na103/Dueottosei/img/GaryAdapter/socket.jpg

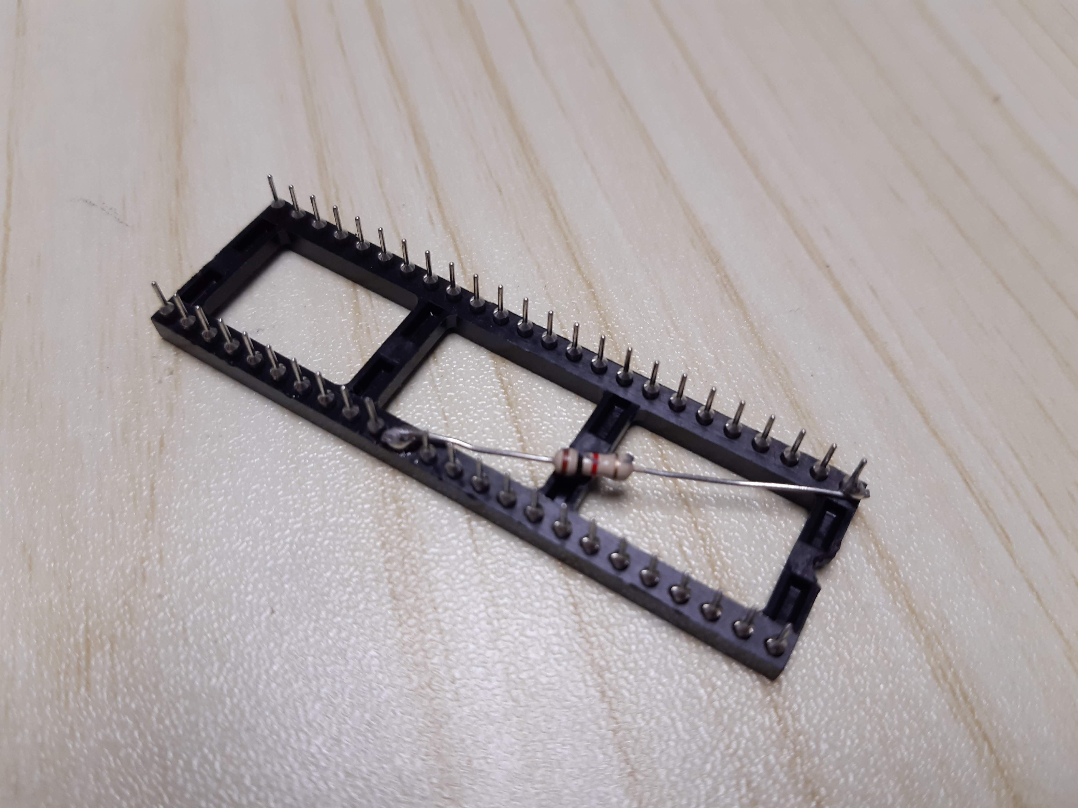
img/GaryAdapter/socket.jpg
