na103/Dueottosei/img/ProgramManager.jpg

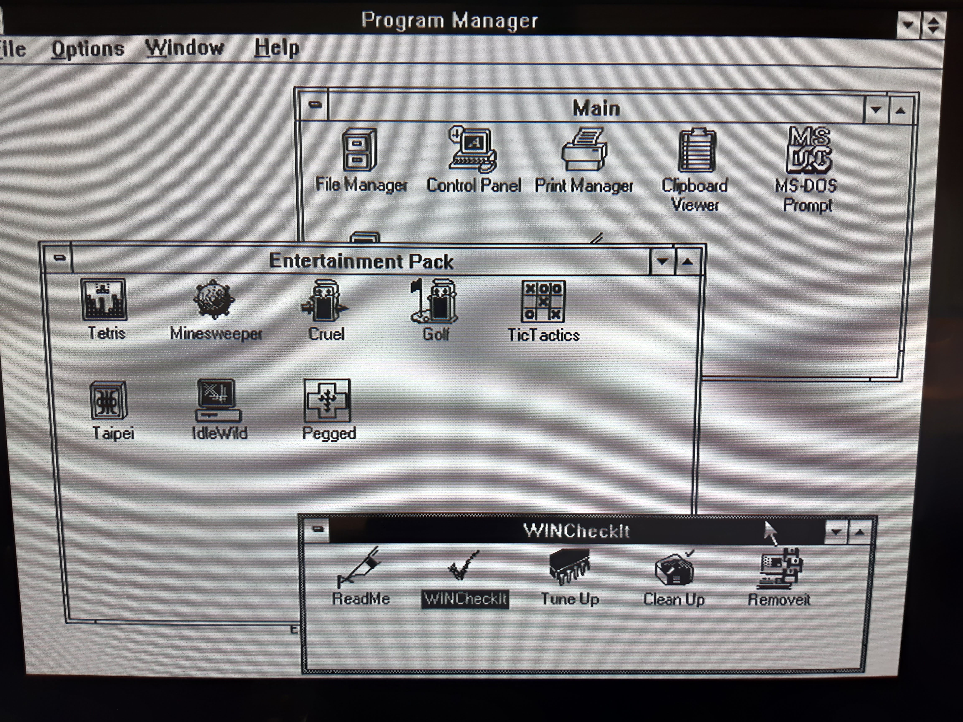
img/ProgramManager.jpg
