na103/Dueottosei/img/routing_B.png

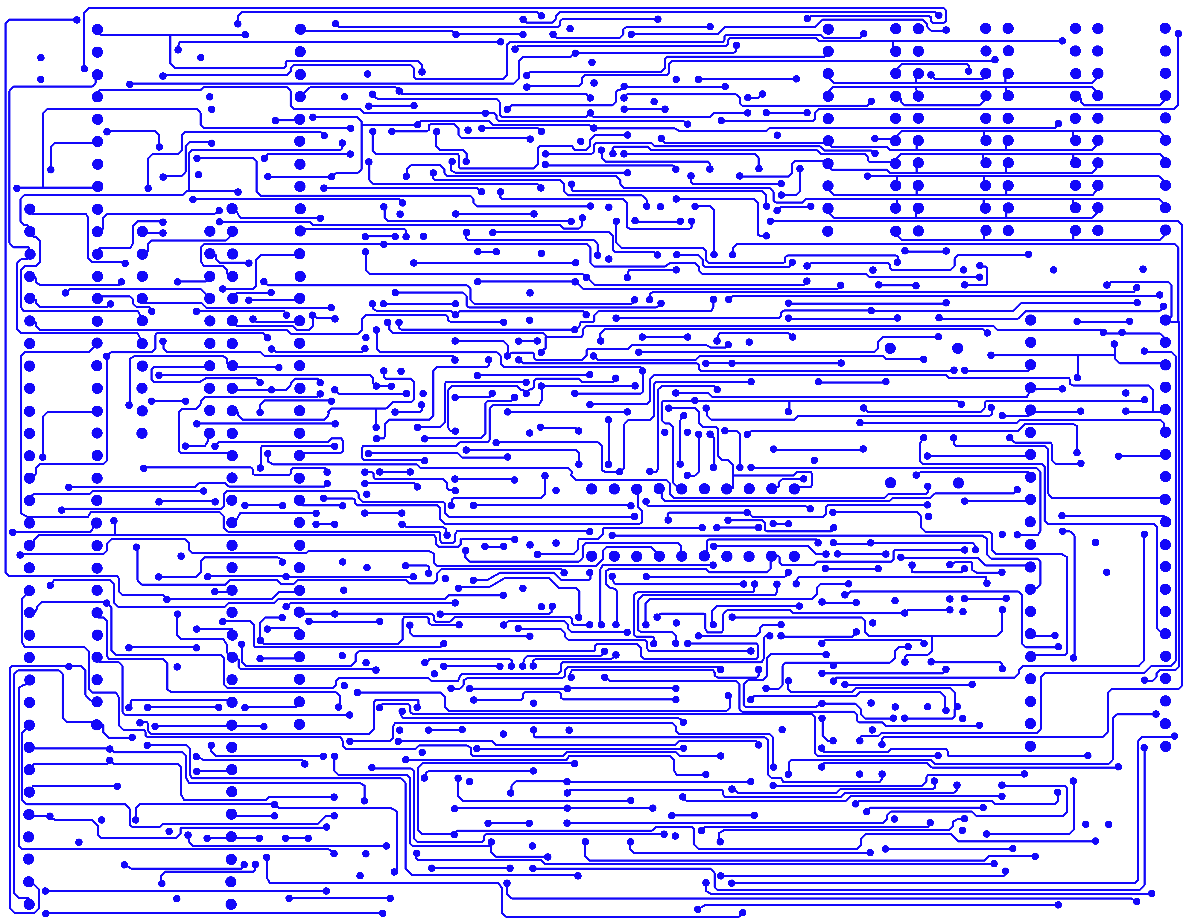
img/routing_B.png
