na103/Dueottosei/img/Wincheckit/cmos.jpg

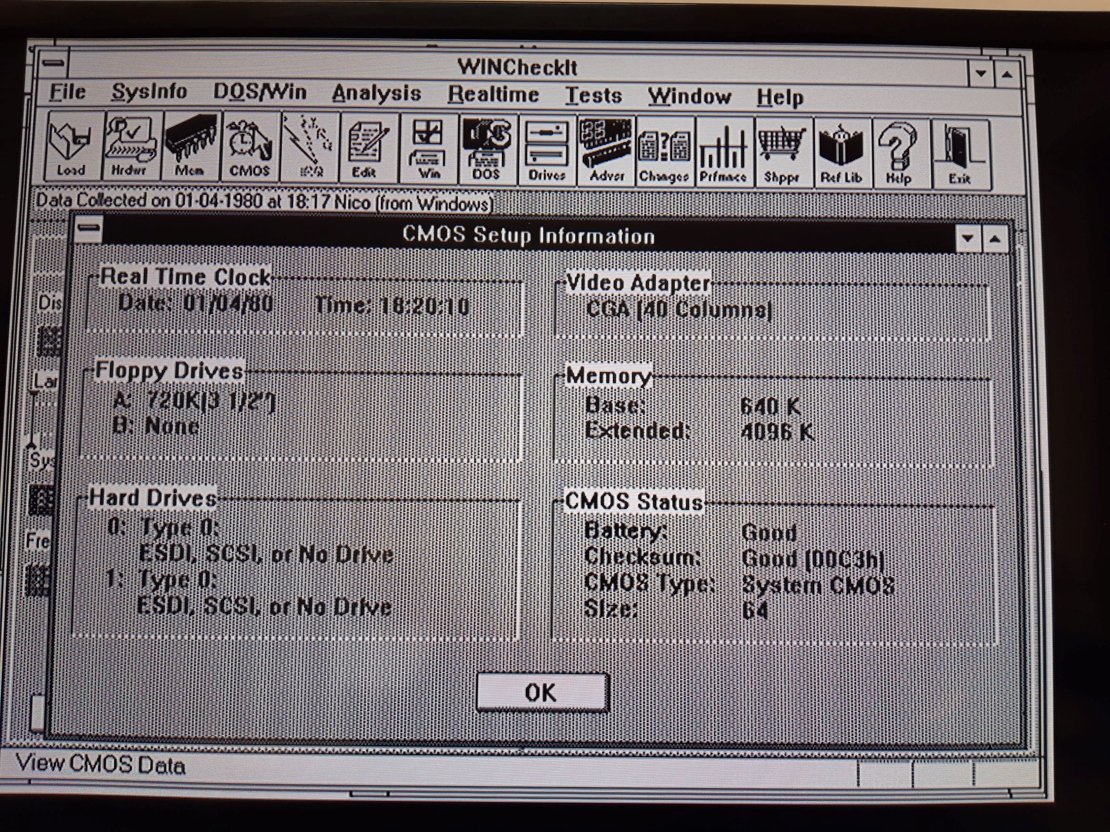
img/Wincheckit/cmos.jpg
