na103/Dueottosei/img/Wincheckit/hw1.jpg

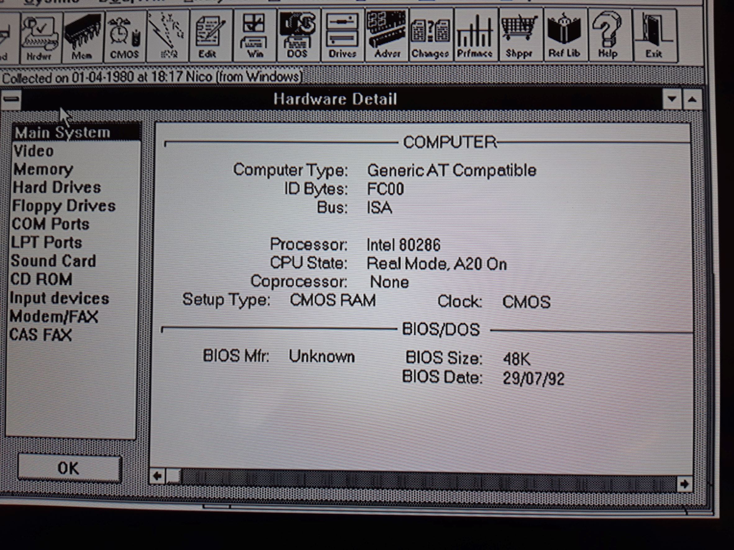
img/Wincheckit/hw1.jpg
