na103/Dueottosei/img/Wincheckit/hw2.jpg

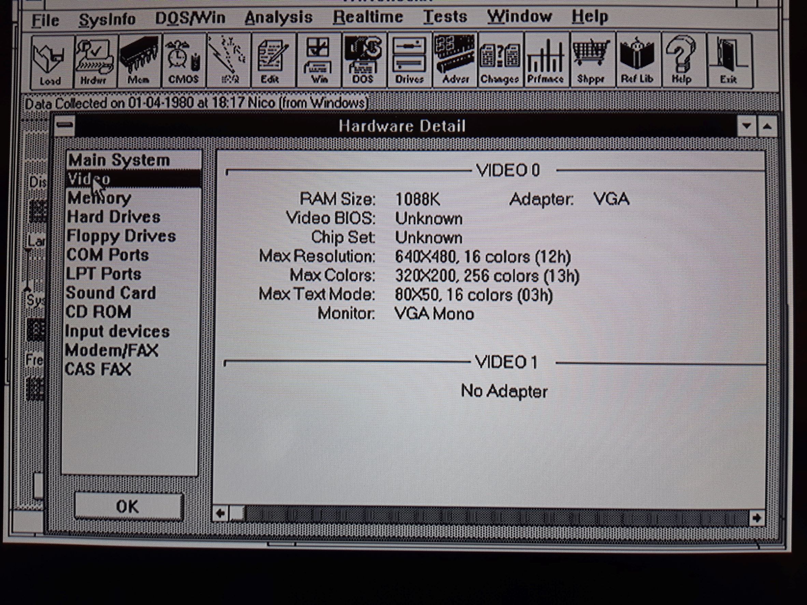
img/Wincheckit/hw2.jpg
