na103/Dueottosei/img/Wincheckit/hw3.jpg

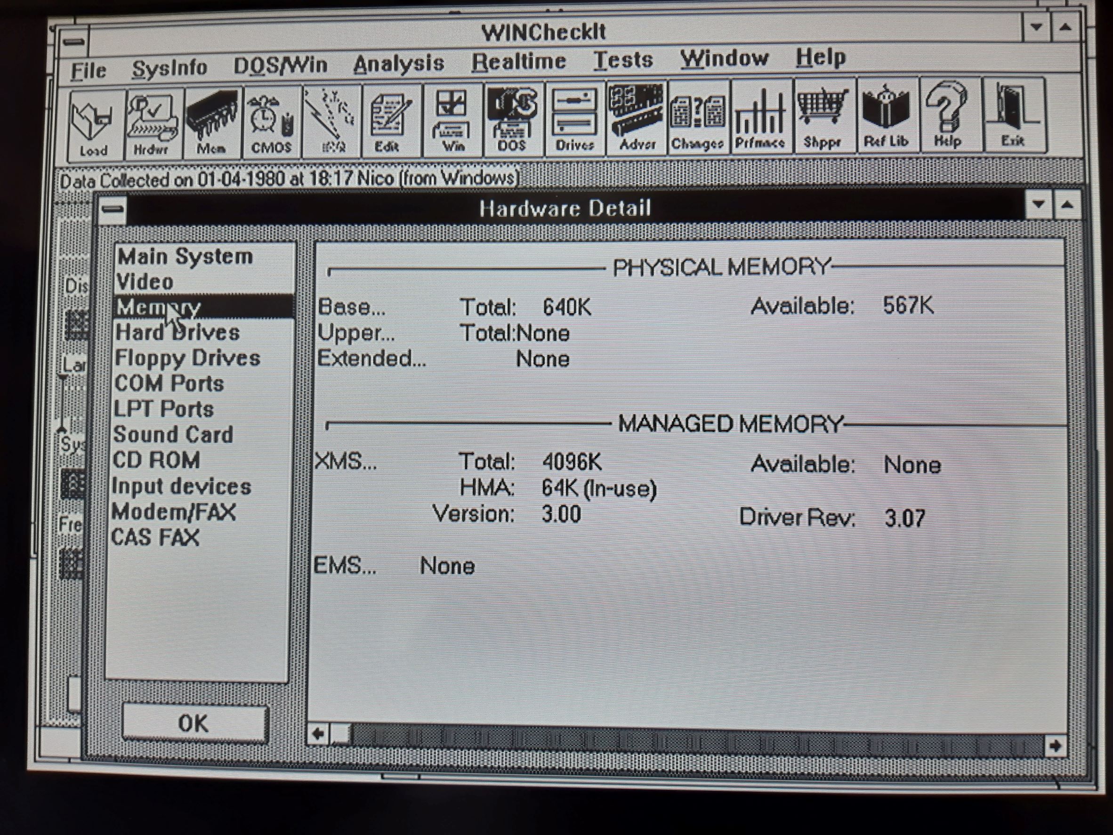
img/Wincheckit/hw3.jpg
