na103/Dueottosei/img/Wincheckit/hw4.jpg

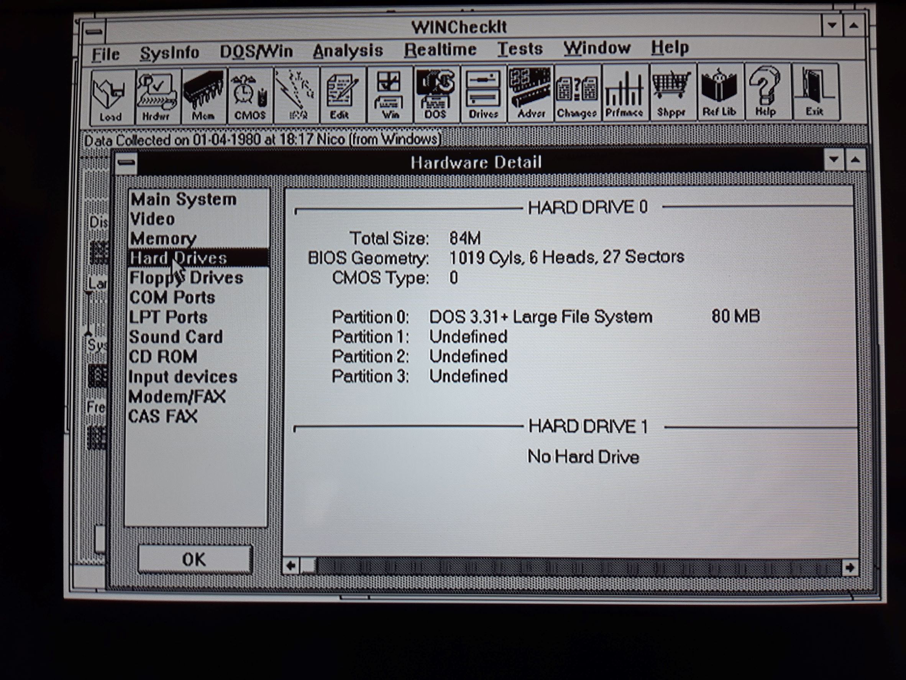
img/Wincheckit/hw4.jpg
