na103/Dueottosei/img/Wincheckit/hw6.jpg

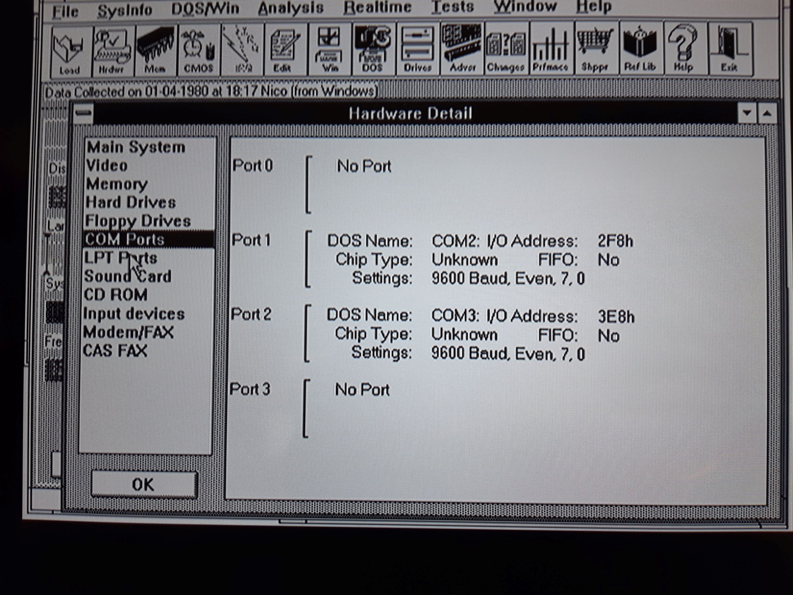
img/Wincheckit/hw6.jpg
