na103/Dueottosei/img/Wincheckit/hw7.jpg

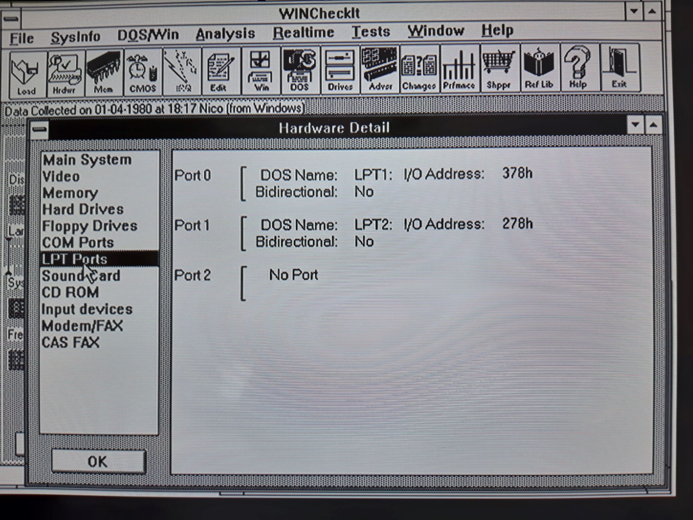
img/Wincheckit/hw7.jpg
