na103/Dueottosei/img/Wincheckit/hw8.jpg

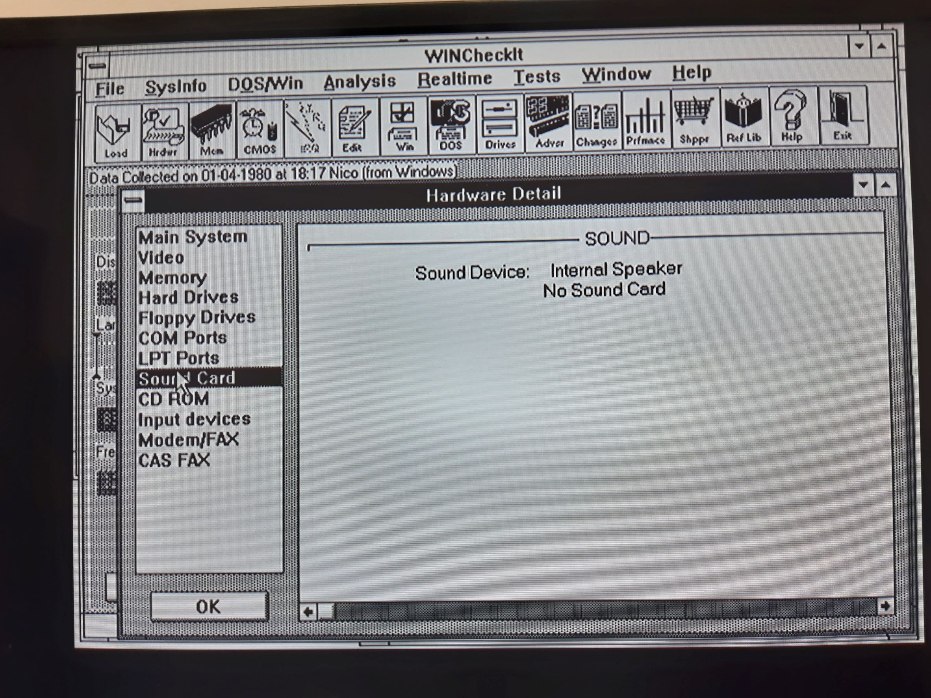
img/Wincheckit/hw8.jpg
