na103/Dueottosei/img/Wincheckit/mem1.jpg

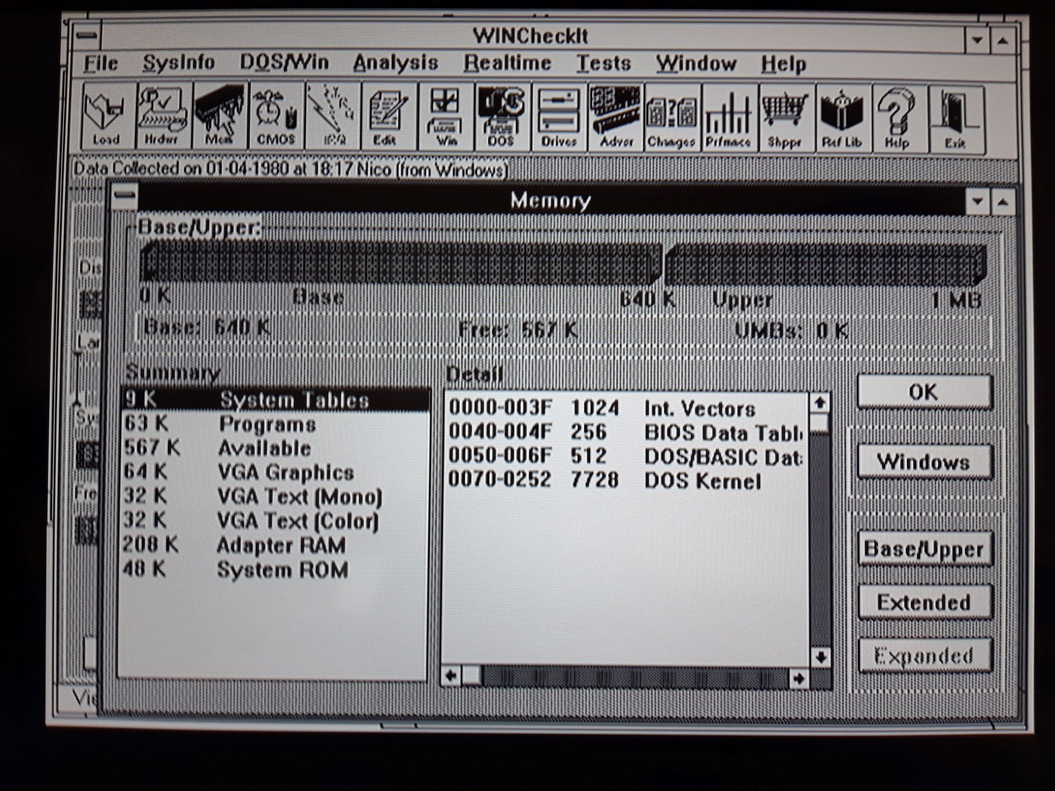
img/Wincheckit/mem1.jpg
