na103/Dueottosei/img/Wincheckit/mem2.jpg

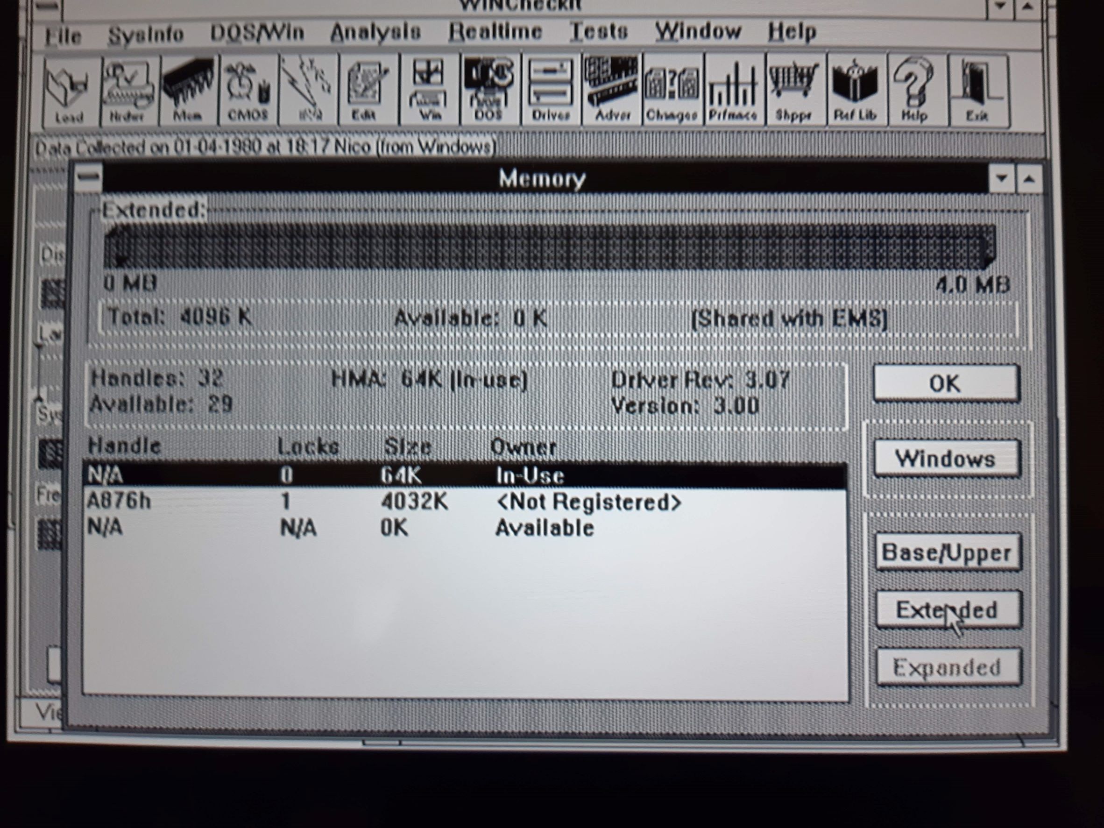
img/Wincheckit/mem2.jpg
