na103/Dueottosei/img/Wincheckit/perf1.jpg

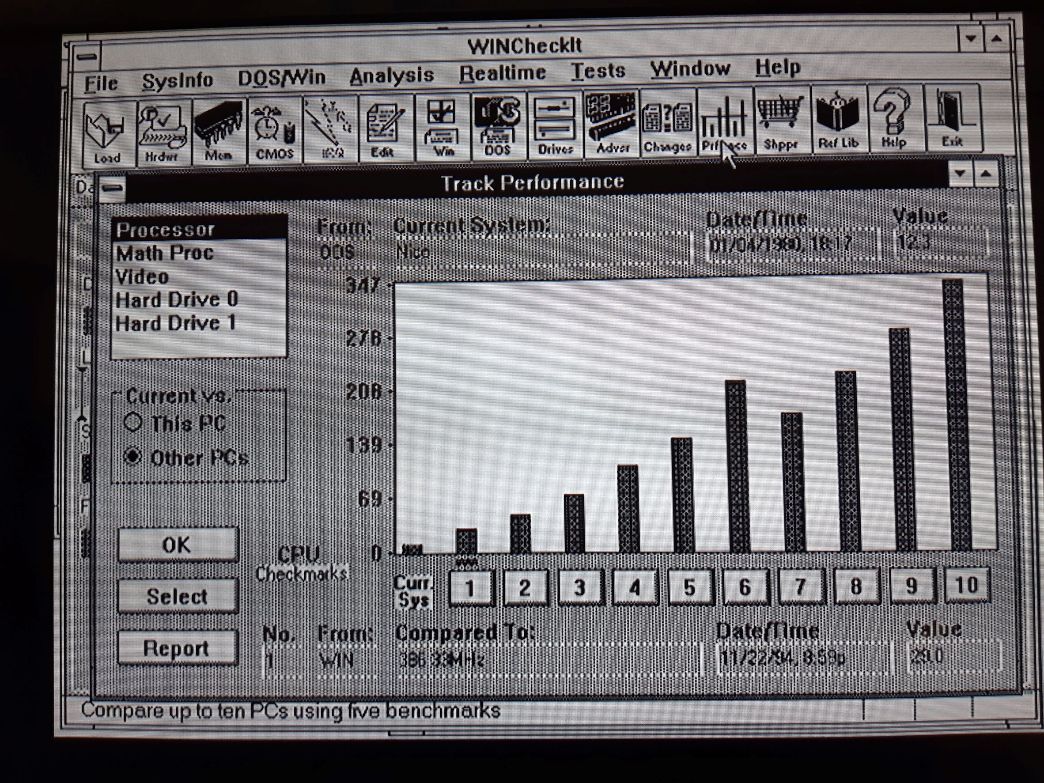
img/Wincheckit/perf1.jpg
