na103/Dueottosei/img/Wincheckit/perf3.jpg

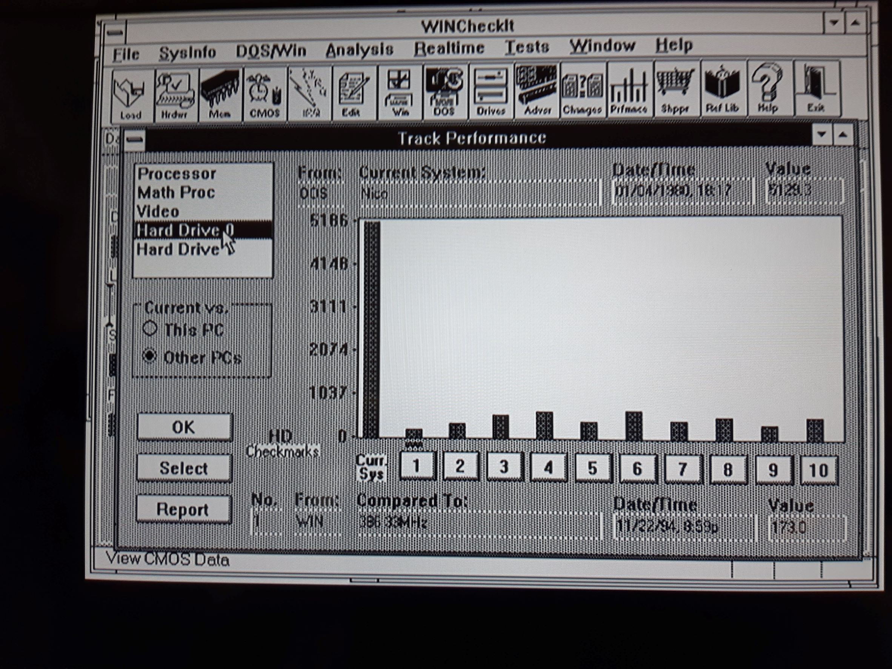
img/Wincheckit/perf3.jpg
