na103/Dueottosei/img/Wincheckit/summary.jpg

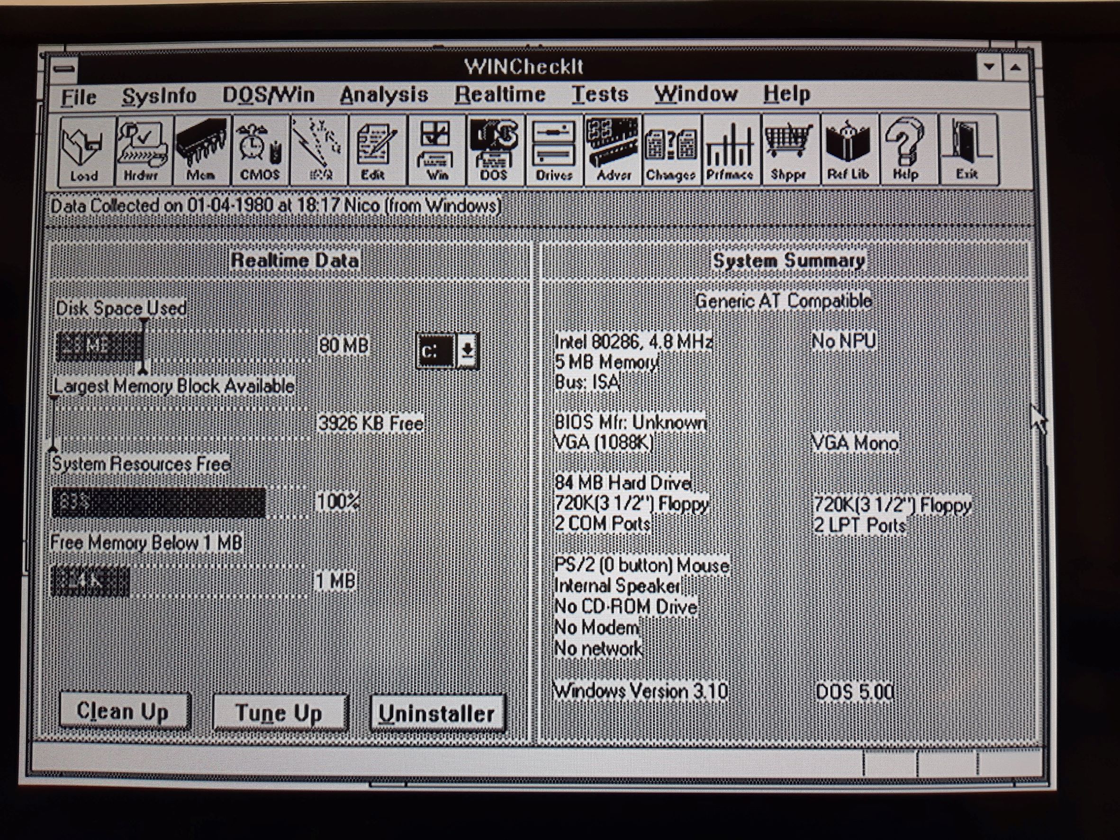
img/Wincheckit/summary.jpg
