na103/Dueottosei/img/Word2.0.jpg

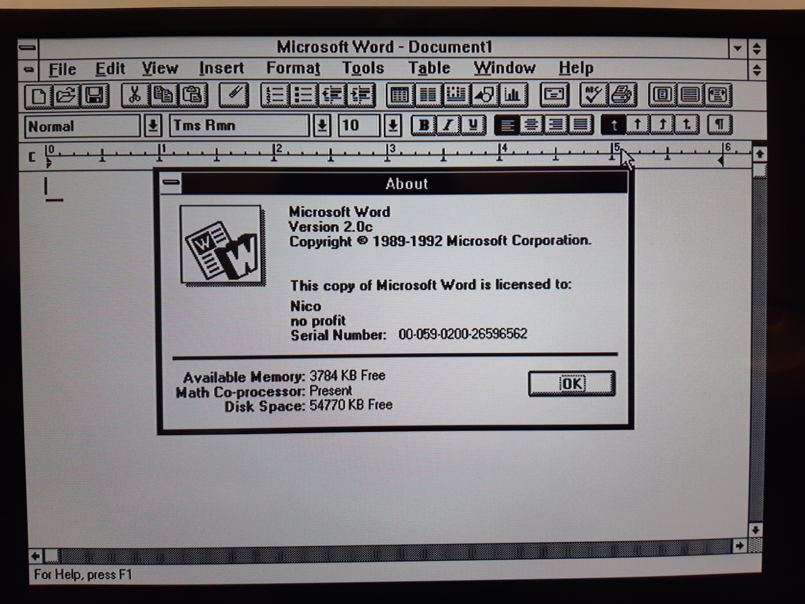
img/Word2.0.jpg
