na103/Dueottosei/img/xc2018_vortex.jpg

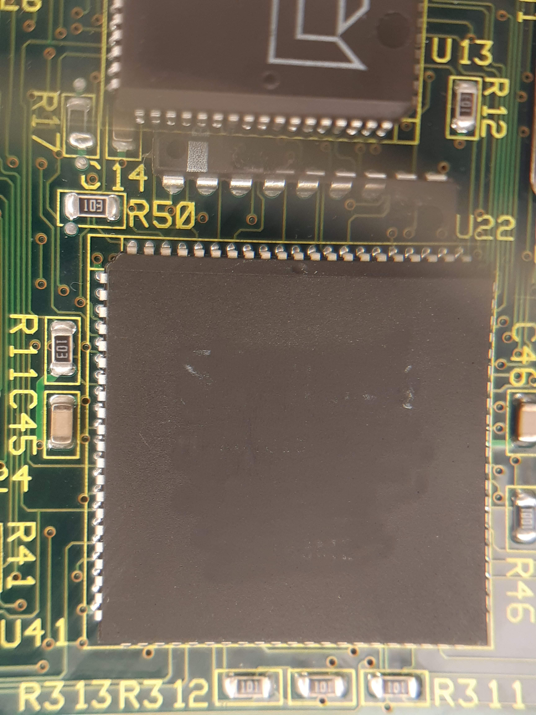
img/xc2018_vortex.jpg
