na103/Dueottosei/img/BuildStep/step1.jpg

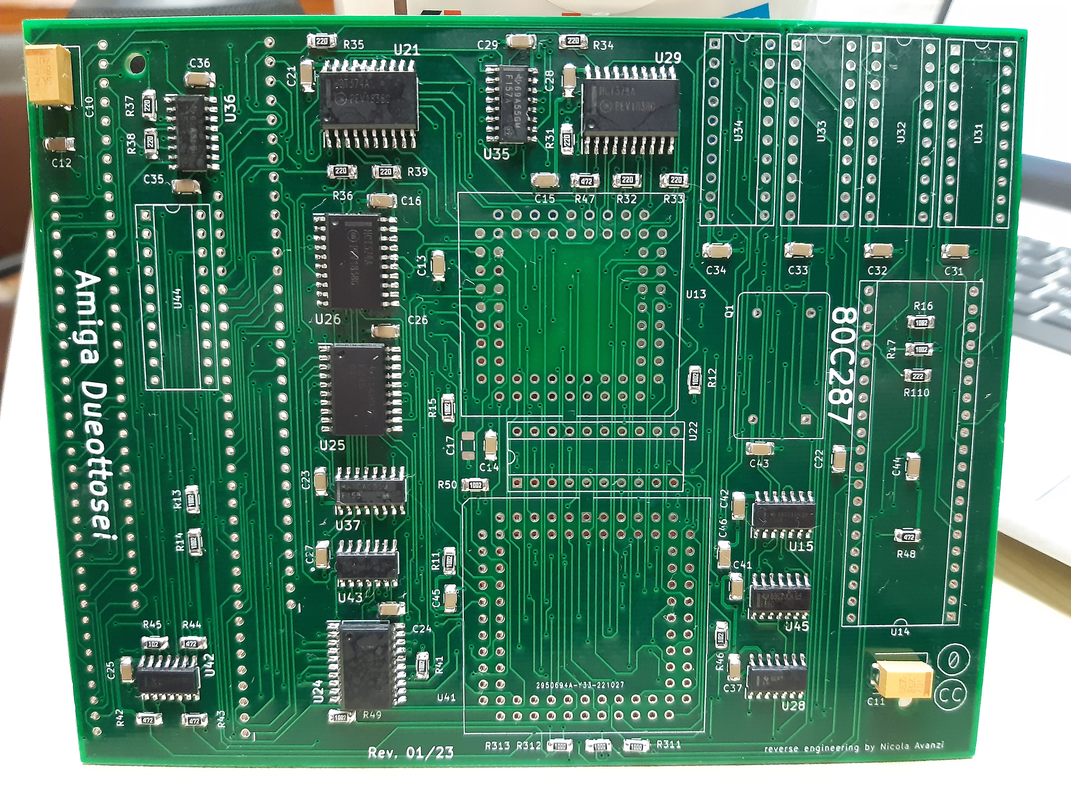
img/BuildStep/step1.jpg
