na103/Dueottosei/img/BuildStep/step2.jpg

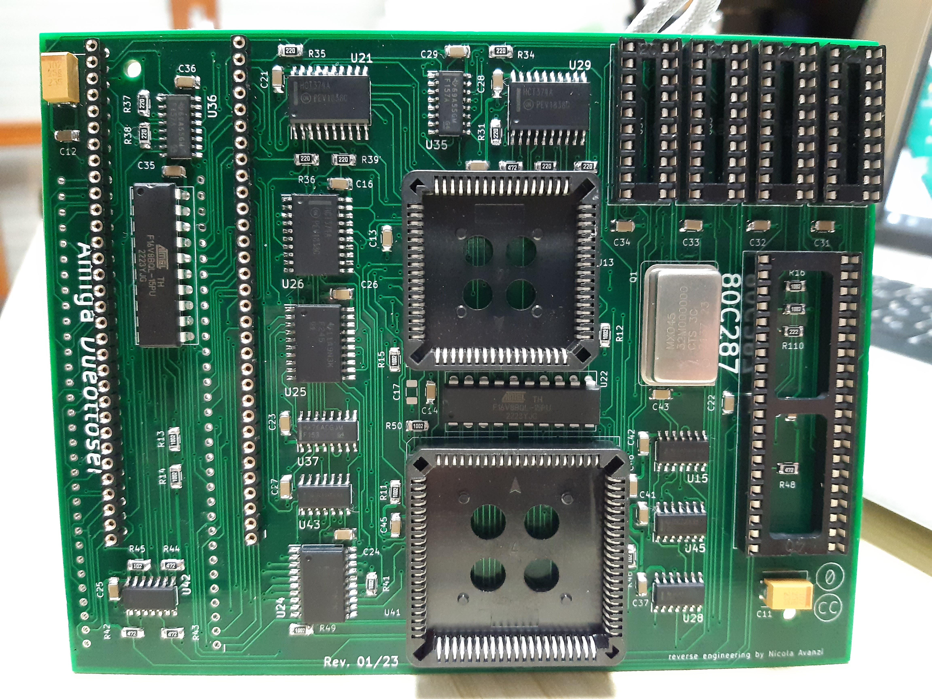
img/BuildStep/step2.jpg
