na103/Dueottosei/img/BuildStep/step3.jpg

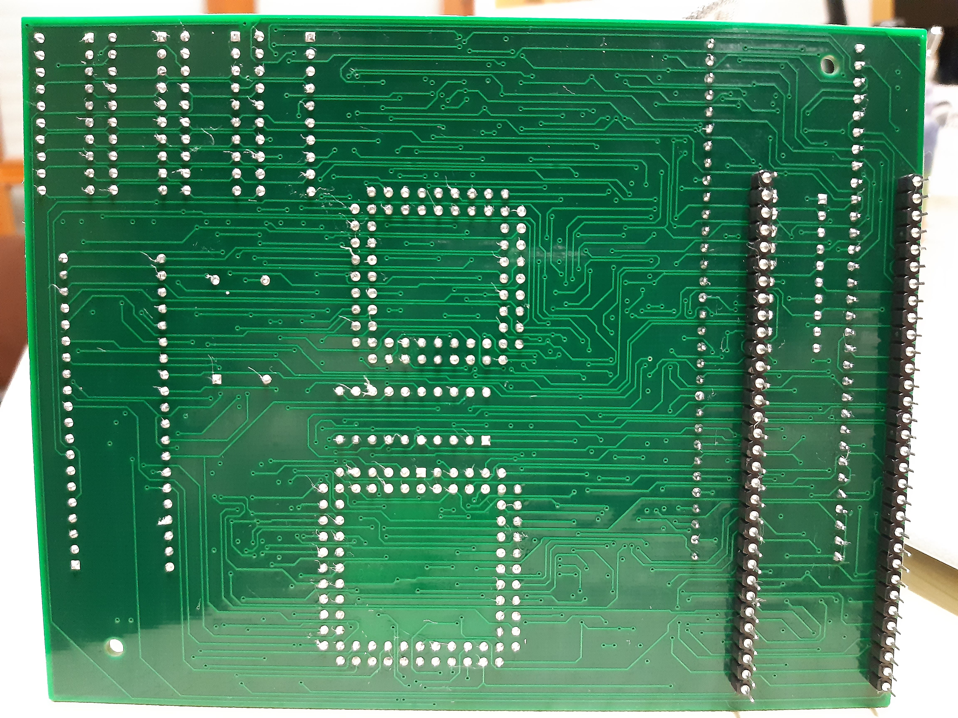
img/BuildStep/step3.jpg
