na103/Dueottosei/img/BuildStep/step4.jpg

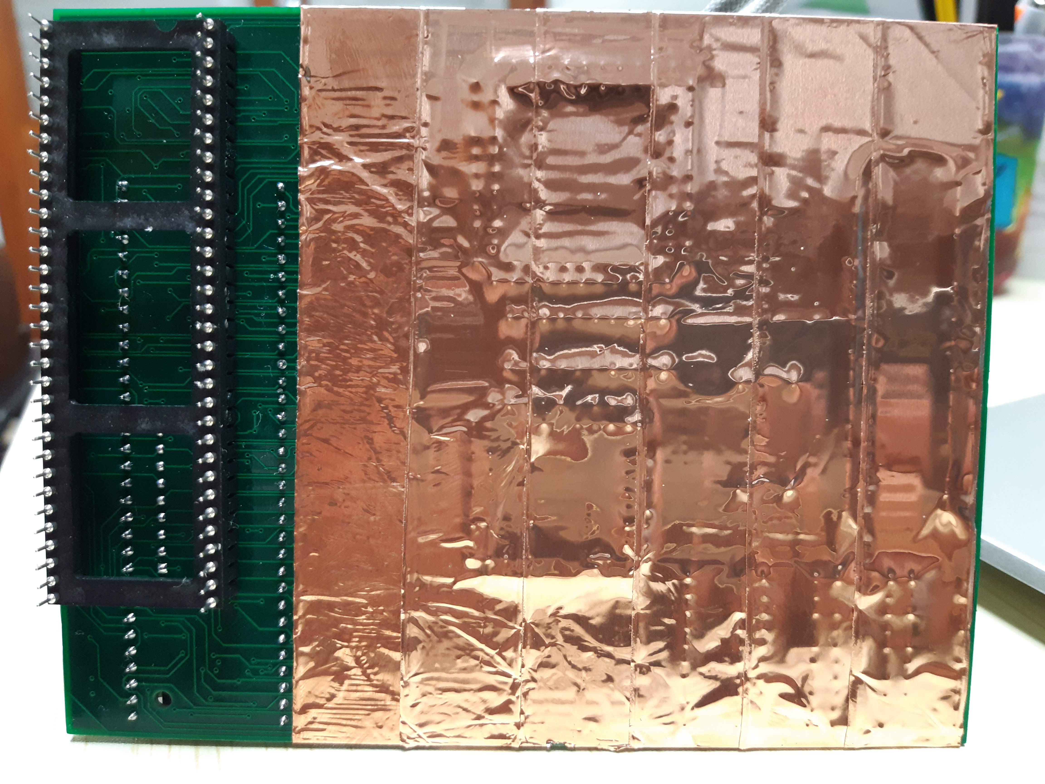
img/BuildStep/step4.jpg
