na103/Dueottosei/kicad/atonceplus/atonceplus.sch

## KiCad design kicad/atonceplus/atonceplus.sch (2022-12-14)

Schematic: atonceplus.sch

Parts:
C10, C11: 100uF; CP_EIA-7361-438_AVX-U
C12, C13, C14, C15, C16, C21, C22, C23, C24, C25, C26, C27, C28, C29, C31, C32, C33, C34, C35, C36, C37, C41, C42, C43, C44, C45, C46: 100nF; C_1206_3216Metric
C17: empty; C_1206_3216Metric
J1: Amiga board 68k socket; DIPS2286W51P254L8128H419Q64N; Manufacturer_Part_Number 110-93-964-41-001000; Mouser Part Number 575-193964
J2: Motorola 68k CPU; DIPS2286W51P254L8128H419Q64N; Manufacturer_Part_Number 110-93-964-41-001000; Mouser Part Number 575-193964
Q1: 32MHz; Oscillator_DIP-14
R11, R12, R13, R14, R15, R16, R17, R41, R49, R50: 10K; R_1206_3216Metric
R31, R32, R33, R34, R35, R36, R37, R38, R39: 22; R_1206_3216Metric
R42, R43, R44, R47, R48: 4.7K; R_1206_3216Metric
R45, R46: 1K; R_1206_3216Metric
R110: 2.2K; R_1206_3216Metric
R311, R312, R313: 100; R_1206_3216Metric
U13: N80C286-16; PLCC-68
U14: 80C287; DIP-40_W15.24mm_Socket
U15: 74LS08; SOIC127P600X175-14N
U21, U26, U29: 74HCT374; SOIC127P1030X265-20N
U22, U44: GAL16V8; DIP-20_W7.62mm
U24, U25: SN74F245DWR; SOIC127P1030X265-20N; Manufacturer_Part_Number SN74F245DWR; Mouser Part Number 595-SN74F245DWR
U28: SN74F86D; SOIC127P600X175-14N; Manufacturer_Part_Number SN74F86D; Mouser Part Number 595-SN74F86D
U31, U32, U33, U34: TMS44C256-80; DIP-20_W7.62mm
U35, U36: SN74F157AD; SOIC127P600X175-16N; Manufacturer_Part_Number SN74F157AD; Mouser Part Number 595-SN74F157AD
U37: SN74F153D; SOIC127P600X175-16N; Manufacturer_Part_Number SN74F153D; Mouser Part Number 595-SN74F153D
U41: XC2018-PC84; PLCC-84
U42: SN74F125D; SOIC127P600X175-14N; Manufacturer_Part_Number SN74F125D; Mouser Part Number 595-SN74F125D
U43: SN74F00D; SOIC127P600X175-14N; Manufacturer_Part_Number SN74F00D; Mouser Part Number 595-SN74F00D
U45: SN74F260D; SOIC127P600X175-14N; Manufacturer_Part_Number SN74F260D; Mouser Part Number 595-SN74F260D

Connections:
6_A0: U13.34 (A0), U21.3 (D0)
6_A1: U13.33 (A1), U21.4 (D1)
6_A2: U13.32 (A2), U21.7 (D2)
6_A3: U13.28 (A3), U21.8 (D3)
6_A4: U13.27 (A4), U21.13 (D4)
6_A5: U13.26 (A5), U21.14 (D5)
6_A6: U13.25 (A6), U21.17 (D6)
6_A7: U13.24 (A7), U21.18 (D7)
6_A8: U13.23 (A8), U29.3 (D0)
6_A9: U13.22 (A9), U29.4 (D1)
6_A10: U13.21 (A10), U29.7 (D2)
6_A11: U13.20 (A11), U29.8 (D3)
6_A12: U13.19 (A12), U29.13 (D4)
6_A13: U13.18 (A13), U29.14 (D5)
6_A14: U13.17 (A14), U29.17 (D6)
6_A15: U13.16 (A15), U29.18 (D7)
6_A16: U13.15 (A16), U41.5
6_A17: U13.14 (A17), U41.84
6_A18: U13.13 (A18), U41.82
6_A19: U13.12 (A19), U41.80, U45.13 (1E)
6_A20: U13.11 (A20), U15.5
6_A21: U13.10 (A21), U41.69, U45.3 (1C), U45.9 (2C)
6_A22: U13.8 (A22), U41.70 (WRT/P70), U45.2 (1B), U45.8 (2B)
6_A23: U13.7 (A23), U28.10 (3B), U41.66 (CS2/P66), U45.1 (1A), U45.4 (2A)
6_COD\~INTA: U13.66 (COD\~INTA), U41.41
6_D0: U13.36 (D0), U14.23 (D0), U22.16 (IO4), U24.18 (B1), U32.1 (DQ1), U41.20
6_D1: U13.38 (D1), U14.22 (D1), U22.17 (I03), U24.17 (B2), U32.2 (DQ2), U41.25
6_D2: U13.40 (D2), U14.21 (D2), U24.16 (B3), U26.2 (O0), U32.18 (DQ3), U41.13
6_D3: U13.42 (D3), U14.20 (D3), U24.15 (B4), U26.5 (O1), U32.19 (DQ4), U41.28
6_D4: U13.44 (D4), U14.19 (D4), U24.14 (B5), U26.6 (O2), U31.1 (DQ1), U41.14
6_D5: U13.46 (D5), U14.18 (D5), U24.13 (B6), U26.9 (O3), U31.2 (DQ2), U41.23
6_D6: U13.48 (D6), U14.17 (D6), U24.12 (B7), U26.12 (O4), U31.18 (DQ3), U41.26
6_D7: U13.50 (D7), U14.16 (D7), U24.11 (B8), U26.15 (O5), U31.19 (DQ4), U41.16
6_D8: U13.37 (D8), U14.15 (D8), U25.18 (B1), U26.16 (O6), U34.1 (DQ1), U41.72 (DIN)
6_D9: U13.39 (D9), U14.14 (D9), U25.17 (B2), U26.19 (O7), U34.2 (DQ2), U41.62 (CS0/P62)
6_D10: U13.41 (D10), U14.12 (D10), U25.16 (B3), U34.18 (DQ3), U41.68
6_D11: U13.43 (D11), U14.11 (D11), U25.15 (B4), U34.19 (DQ4), U41.58
6_D12: U13.45 (D12), U14.8 (D12), U25.14 (B5), U33.1 (DQ1)
6_D13: U13.47 (D13), U14.7 (D13), U25.13 (B6), U33.2 (DQ2)
6_D14: U13.49 (D14), U14.6 (D14), U25.12 (B7), U33.18 (DQ3)
6_D15: U13.51 (D15), U14.5 (D15), U25.11 (B8), U33.19 (DQ4)
6_HDLA: U13.65 (HLDA), U21.1 (OE), U29.1 (OE), U41.59
6_HOLD: U13.64 (HOLD), U41.34 (HDC)
6_INTR: U13.57 (INTR), U41.73 (DOUT)
6_M\~IO: U13.67 (M\~IO), U41.63 (CS1/P63), U43.5 (2B)
6_PEREQ: R110.2, U13.61 (PEREQ), U14.24 (PEREQ)
6_RESET: R47.2, U13.29 (RESET), U41.21
6_~BHE: U13.1 (~BHE), U41.18
6_~BUSY: U13.54 (~BUSY), U41.60
6_~PEACK: U13.6 (~PEACK), U14.36 (~PEACK)
6_~READY: U13.63 (~READY), U41.40
6_~S0: R11.1, U13.5 (~S0), U41.6, U43.9 (3A)
6_~S1: R12.2, U13.4 (~S1), U41.15, U43.10 (3B)
7_NPS2: U14.33 (NPS2), U22.19 (IO1), U41.55 (DONE/PROG)
7_RESET: R48.2, U14.35 (RESET), U41.51
7_~BUSY: R17.2, U14.25 (~BUSY), U41.57
7_~ERROR: R16.2, U14.26 (~ERROR), U41.52
7_~NPRD: U14.27 (~NPRD), U44.14 (IO6)
7_~NPS1: U14.34 (~NPS1), U41.35, U44.12 (IO8)
7_~NPWR: U14.28 (~NPWR), U44.13 (IO7)
CLK: U22.12 (IO8), U41.50, U41.74 (CLK)
GCLK: U21.11 (Cp), U29.11 (Cp), U41.11 (P11/GCLK), U43.8 (3Y)
GND: C10.2, C11.2, C12.2, C13.2, C14.2, C15.2, C16.2, C17.2, C21.2, C22.2, C23.2, C24.2, C25.2, C26.2, C27.2, C28.2, C29.2, C31.2, C32.2, C33.2, C34.2, C35.2, C36.2, C37.2, C41.2, C42.2, C43.2, C44.2, C45.2, C46.2, J1.16, J1.53, J2.16, J2.53, Q1.7 (GND), R110.1, U13.9 (VSS), U13.35 (VSS), U13.59 (NMI), U13.60 (VSS), U14.10 (VSS), U14.30 (VSS), U14.39 (CKM), U15.7 (GND), U21.10 (GND), U22.10 (GND), U24.10 (GND), U25.10 (GND), U26.10 (GND), U28.5 (2B), U28.7 (GND), U28.12 (4A), U28.13 (4B), U29.10 (GND), U31.16 (~G), U31.20 (VSS), U32.16 (~G), U32.20 (VSS), U33.16 (~G), U33.20 (VSS), U34.16 (~G), U34.20 (VSS), U35.8 (GN_D), U35.15 (~G), U36.8 (GN_D), U36.15 (~G), U37.1 (1~G), U37.8 (GND), U37.15 (2~G), U41.1 (GND), U41.43 (GND), U42.7 (GND), U43.7 (GND), U44.10 (GND), U45.7 (GND), U45.11 (2E)
LDC: U24.19 (~OE), U25.19 (~OE), U41.36 (LDC)
M2: R41.2, U24.1 (DIR), U25.1 (DIR), U41.33 (M2)
M_~AS: J2.6, R42.2, U41.8, U42.2 (1A)
M_~BG: J2.11, U37.5 (1C1), U37.6 (1C0)
M_~BGACK: J2.12, U44.15 (IO5)
M_~BR: J2.13, U44.16 (IO4)
M_~DTACK: J2.10, R45.2, U41.37, U42.11 (4Y)
M_~LDS: J2.8, R43.2, U15.1, U41.10, U42.5 (2A)
M_~UDS: J2.7, R44.2, U15.2, U41.3, U42.9 (3A)
unnamed: C17.1, U13.52 (NC)
unnamed: Q1.8 (OUT), U13.31 (CLK), U14.32 (CLK), U28.1 (1A)
unnamed: R15.2, U13.53 (~ERROR)
unnamed: R31.1, U31.6 (A0), U32.6 (A0), U33.6 (A0), U34.6 (A0)
unnamed: R31.2, U35.12 (4Y)
unnamed: R32.1, U31.7 (A1), U32.7 (A1), U33.7 (A1), U34.7 (A1)
unnamed: R32.2, U35.9 (3Y)
unnamed: R33.1, U31.8 (A2), U32.8 (A2), U33.8 (A2), U34.8 (A2)
unnamed: R33.2, U35.7 (2Y)
unnamed: R34.1, U31.9 (A3), U32.9 (A3), U33.9 (A3), U34.9 (A3)
unnamed: R34.2, U35.4 (1Y)
unnamed: R35.1, U36.12 (4Y)
unnamed: R35.2, U31.11 (A4), U32.11 (A4), U33.11 (A4), U34.11 (A4)
unnamed: R36.1, U36.9 (3Y)
unnamed: R36.2, U31.12 (A5), U32.12 (A5), U33.12 (A5), U34.12 (A5)
unnamed: R37.1, U36.7 (2Y)
unnamed: R37.2, U31.13 (A6), U32.13 (A6), U33.13 (A6), U34.13 (A6)
unnamed: R38.1, U36.4 (1Y)
unnamed: R38.2, U31.14 (A7), U32.14 (A7), U33.14 (A7), U34.14 (A7)
unnamed: R39.1, U37.9 (2Y)
unnamed: R39.2, U31.15 (A8), U32.15 (A8), U33.15 (A8), U34.15 (A8)
unnamed: R311.2, U31.4 (~RAS), U32.4 (~RAS), U33.4 (~RAS), U34.4 (~RAS)
unnamed: R312.2, U31.17 (~CAS), U32.17 (~CAS)
unnamed: R313.2, U33.17 (~CAS), U34.17 (~CAS)
unnamed: U15.8, U35.1 (~A~/B), U36.1 (~A~/B), U37.14 (A)
unnamed: U15.10, U15.11
unnamed: U28.9 (3A), U45.6 (2Y)
unnamed: U37.2 (B), U44.19 (IO1)
unnamed: U42.1 (1~OE), U42.4 (2~OE), U42.10 (3~OE), U43.3 (1Y)
unnamed: U43.4 (2A), U45.5 (1Y)
P9: R50.2, U41.9, U44.9 (I9)
P19: U21.2 (O0), U22.7 (I7), U41.19
P24: U41.24, U43.6 (2Y)
P27: U28.6 (2Y), U41.27
P29: U41.29, U44.1 (I1/CLK)
P30: U15.4, U41.30
P38: R312.1, U41.38
P39: R313.1, U41.39
P42: U41.42, U43.11 (4Y)
P45: U22.1 (I1/CLK), U26.11 (Cp), U41.45
P46: R49.2, U41.46, U44.17 (I03)
P47: U22.13 (IO7), U41.47
P48: R311.1, U15.12, U41.48
P53: U22.11 (I10/~OE~), U22.14 (IO6), U26.1 (OE), U41.53 (XTL2(I)/P53)
P56: U28.3 (1Y), U41.56 (XTL1(O)/P56)
P61: U15.3, U22.6 (I6), U41.61
P65: R46.2, U41.65, U43.1 (1A)
P67: U28.8 (3Y), U41.67
P71: U15.6, U41.71, U45.10 (2D), U45.12 (1D)
VCC: C10.1, C11.1, C12.1, C13.1, C14.1, C15.1, C16.1, C21.1, C22.1, C23.1, C24.1, C25.1, C26.1, C27.1, C28.1, C29.1, C31.1, C32.1, C33.1, C34.1, C35.1, C36.1, C37.1, C41.1, C42.1, C43.1, C44.1, C45.1, C46.1, J1.14, J1.49, J2.14, J2.49, Q1.14 (Vcc), R11.2, R12.1, R13.1, R14.1, R15.1, R16.1, R17.1, R41.1, R42.1, R43.1, R44.1, R45.1, R46.1, R47.1, R48.1, R49.1, R50.1, U13.30 (VCC), U13.62 (VCC), U14.9 (VCC), U15.9, U15.13, U15.14 (VCC), U21.20 (VCC), U22.20 (VCC), U24.20 (VCC), U25.20 (VCC), U26.20 (VCC), U28.2 (1B), U28.14 (VCC), U29.20 (VCC), U31.10 (VCC), U32.10 (VCC), U33.10 (VCC), U34.10 (VCC), U35.16 (VCC), U36.16 (VCC), U37.3 (1C3), U37.4 (1C2), U37.16 (VCC), U41.12 (PWRDWN), U41.22 (VCC), U41.31 (M1), U41.32 (M0), U41.64 (VCC), U42.14 (VCC), U43.14 (VCC), U44.20 (VCC), U45.14 (VCC)
Z_A1: J1.29, J2.29, U14.29 (CMD0), U21.5 (O1), U22.9 (I9), U35.13 (4B), U41.17
Z_A2: J1.30, J2.30, U14.31 (CMD1), U21.6 (O2), U26.3 (D0), U35.10 (3B)
Z_A3: J1.31, J2.31, U21.9 (O3), U26.4 (D1), U35.6 (2B), U44.2 (I2)
Z_A4: J1.32, J2.32, U21.12 (O4), U26.7 (D2), U35.3 (1B)
Z_A5: J1.33, J2.33, U21.15 (O5), U26.8 (D3), U36.13 (4B), U44.4 (I4)
Z_A6: J1.34, J2.34, U21.16 (O6), U22.2 (I2), U26.13 (D4), U36.10 (3B), U44.5 (I5)
Z_A7: J1.35, J2.35, U21.19 (O7), U22.3 (I3), U26.14 (D5), U36.6 (2B), U44.6 (I6)
Z_A8: J1.36, J2.36, U26.17 (D6), U29.2 (O0), U36.3 (1B), U44.7 (I7)
Z_A9: J1.37, J2.37, U26.18 (D7), U29.5 (O1), U37.11 (2C1), U37.13 (2C3), U44.8 (I8)
Z_A10: J1.38, J2.38, U29.6 (O2), U35.14 (4A)
Z_A11: J1.39, J2.39, U29.9 (O3), U35.11 (3A)
Z_A12: J1.40, J2.40, U29.12 (O4), U35.5 (2A)
Z_A13: J1.41, J2.41, U29.15 (O5), U35.2 (1A)
Z_A14: J1.42, J2.42, U29.16 (O6), U36.14 (4A)
Z_A15: J1.43, J2.43, U22.4 (I4), U29.19 (O7), U36.11 (3A)
Z_A16: J1.44, J2.44, U36.5 (2A), U41.4
Z_A17: J1.45, J2.45, U36.2 (1A), U41.83
Z_A18: J1.46, J2.46, U37.10 (2C0), U37.12 (2C2), U41.81
Z_A19: J1.47, J2.47, U41.79
Z_A20: J1.48, J2.48, U41.78
Z_A21: J1.50, J2.50, U41.77
Z_A22: J1.51, J2.51, U41.76
Z_A23: J1.52, J2.52, U41.75
Z_CLK: J1.15, J2.15, U28.4 (2A)
Z_D0: J1.5, J2.5, U25.2 (A1)
Z_D1: J1.4, J2.4, U25.3 (A2)
Z_D2: J1.3, J2.3, U25.4 (A3)
Z_D3: J1.2, J2.2, U25.5 (A4)
Z_D4: J1.1, J2.1, U22.18 (IO2), U25.6 (A5)
Z_D5: J1.64, J2.64, U25.7 (A6)
Z_D6: J1.63, J2.63, U25.8 (A7)
Z_D7: J1.62, J2.62, U25.9 (A8)
Z_D8: J1.61, J2.61, U24.2 (A1)
Z_D9: J1.60, J2.60, U24.3 (A2)
Z_D10: J1.59, J2.59, U24.4 (A3)
Z_D11: J1.58, J2.58, U24.5 (A4)
Z_D12: J1.57, J2.57, U24.6 (A5)
Z_D13: J1.56, J2.56, U24.7 (A6)
Z_D14: J1.55, J2.55, U24.8 (A7)
Z_D15: J1.54, J2.54, U24.9 (A8)
Z_E: J1.20, J2.20
Z_FC0: J1.28, J2.28
Z_FC1: J1.27, J2.27, U41.7
Z_FC2: J1.26, J2.26
Z_R~W: J1.9, J2.9, U22.8 (I8), U31.3 (~W), U32.3 (~W), U33.3 (~W), U34.3 (~W), U41.2, U41.49, U44.3 (I3)
Z_~AS: J1.6, U42.3 (1Y)
Z_~BERR: J1.22, J2.22
Z_~BG: J1.11, U37.7 (1Y)
Z_~BGACK: J1.12, R13.2, U43.2 (1B), U44.11 (I10/~OE~)
Z_~BR: J1.13, R14.2, U44.18 (IO2)
Z_~DTACK: J1.10, U42.12 (4A), U42.13 (4~OE)
Z_~HALT: J1.17, J2.17
Z_~IPL0: J1.25, J2.25, U43.12 (4A)
Z_~IPL1: J1.24, J2.24, U43.13 (4B)
Z_~IPL2: J1.23, J2.23, U41.44
Z_~LDS: J1.8, U42.6 (2Y)
Z_~RESET: J1.18, J2.18, U41.54 (RESET)
Z_~UDS: J1.7, U42.8 (3Y)
Z_~VMA: J1.19, J2.19
Z_~VPA: J1.21, J2.21, U22.5 (I5)

Notes on the sheet:
LDC low during configuration
DIR H A data to B bus
M0 M1 M2 PWRDWN +5V LCA in SLAVE mode
Data Bit 0 Bus Zorro -->
!7_~NPS1~ = P29 & Z_A5 & Z_A6 & Z_A7 & !Z_A8 & !Z_A9 & !P9 !7_~NPWR~ = P29 & Z_A3 & !Z_R~W~ & Z_A5 & Z_A6 & Z_A7 & !Z_A8 & !Z_A9 & !P9 !7_~NPRD~ = P29 & Z_A3 & Z_R~W~ & Z_A5 & Z_A6 & Z_A7 & !Z_A8 & !Z_A9 & !P9 M_~BGACK~ = P9 & Z_~BGACK~ M_~BR~ = P46 & Z_~BR~ !O19 = P9 & P46
7_NPS2 = !io15 !Z_D4 = gnd 6_D1.D = Z_A1 6_D0.D = P19 io15 = Z_D4 & !Z_R~W~ & !CLK # io15 & CLK # io15 & Z_R~W~ !P53 = Z_R~W~ & !P47 !P47 = !Z_A6 & Z_A7 & Z_A15 & !Z_~VPA~ & !P61 !CLK = Z_A6 & !Z_A7 & Z_A15 & !Z_~VPA~ & !P61
