na103/Dueottosei/xc2018/verilog/dueottosei/clb/clb_aa.v

module clb_aa(
	input b,
	input k,
	input rst,
	output y
);
	
	wire f;
	reg q;
	
	assign f = b;
	
	always @(posedge k, negedge rst) begin
		if (rst == 1'b0) begin
			q <= 1'b0;
		end else begin
			q <= f;
		end
	end
	
	assign y = q;

endmodule
