na103/Dueottosei/img/atonce+.jpg

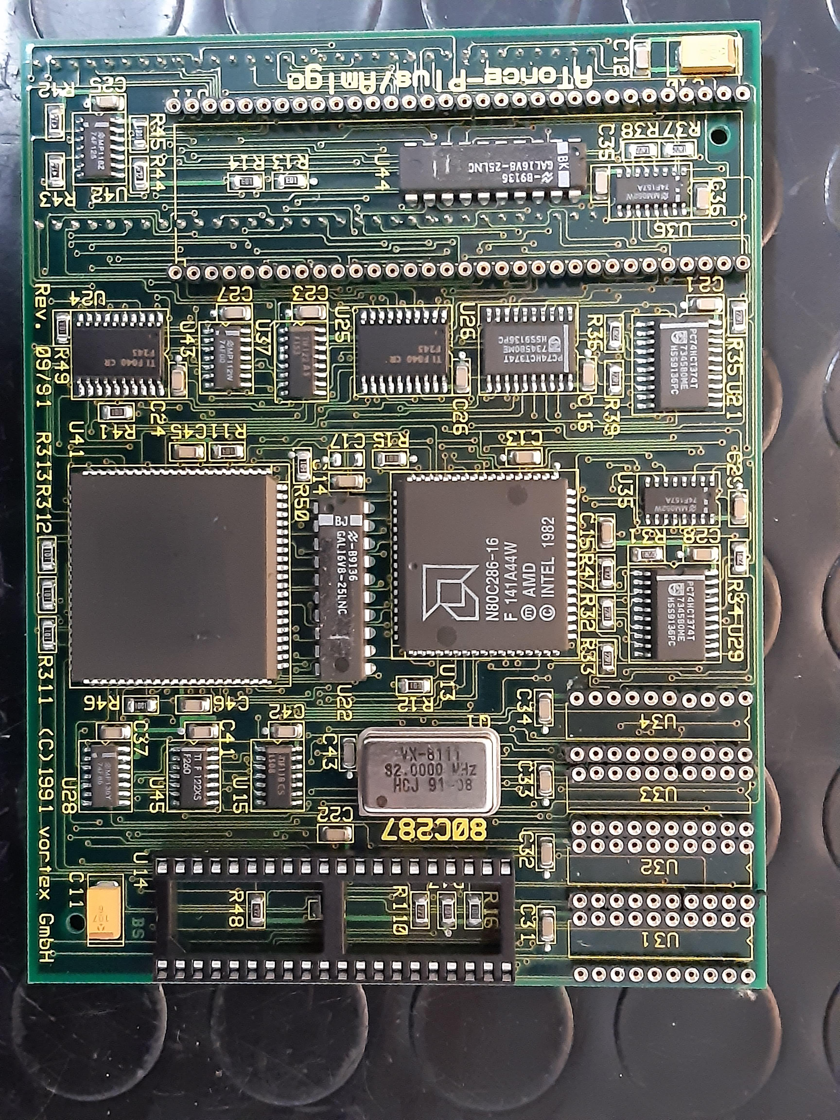
img/atonce+.jpg
